AugustoS97/BMS-BatterySystem/Diseno-Electronico/CAN2Serial/RENDER/render_2.png

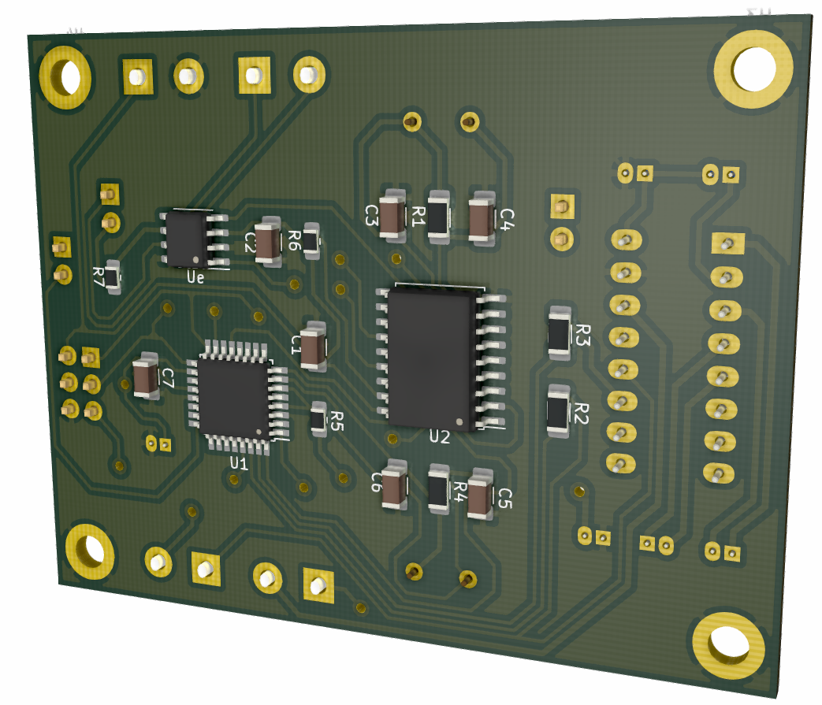
Diseno-Electronico/CAN2Serial/RENDER/render_2.png
