AugustoS97/BMS-BatterySystem/Diseno-Electronico/EPSolar-CAN/RENDER/render_2.png

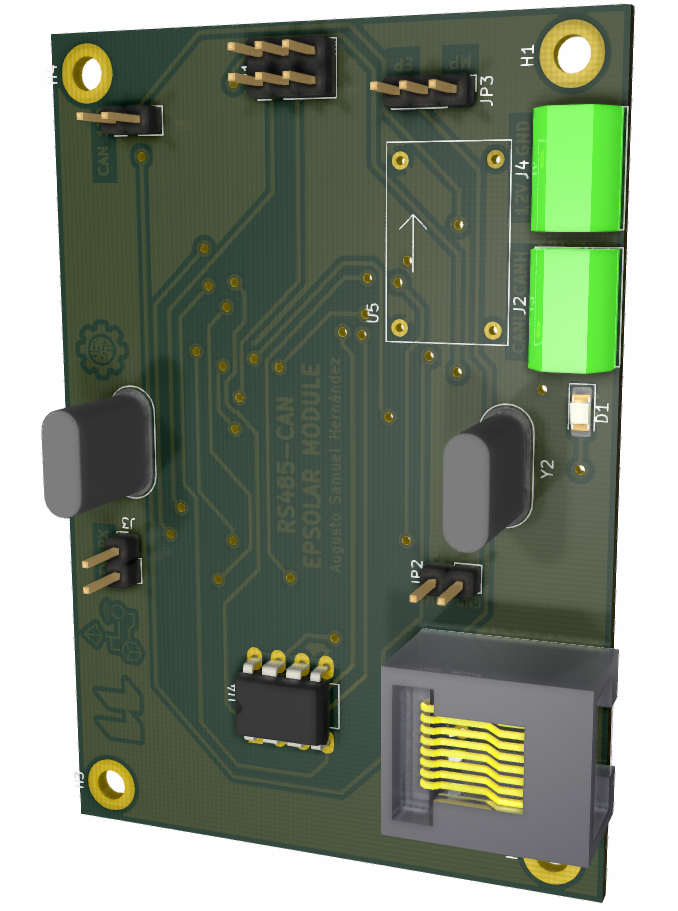
Diseno-Electronico/EPSolar-CAN/RENDER/render_2.png
