AugustoS97/BMS-BatterySystem/Diseno-Electronico/SmartBMS/RENDER/bms_render_top.png

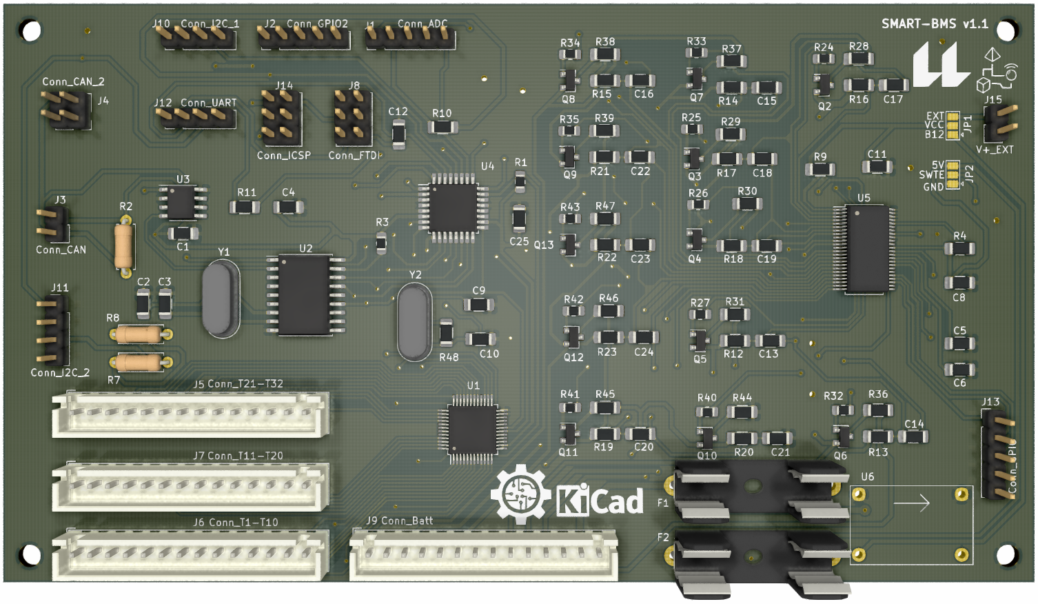
Diseno-Electronico/SmartBMS/RENDER/bms_render_top.png
