AugustoS97/BMS-BatterySystem/Diseno-Electronico/SmartBMS/RENDER/render_0.jpg

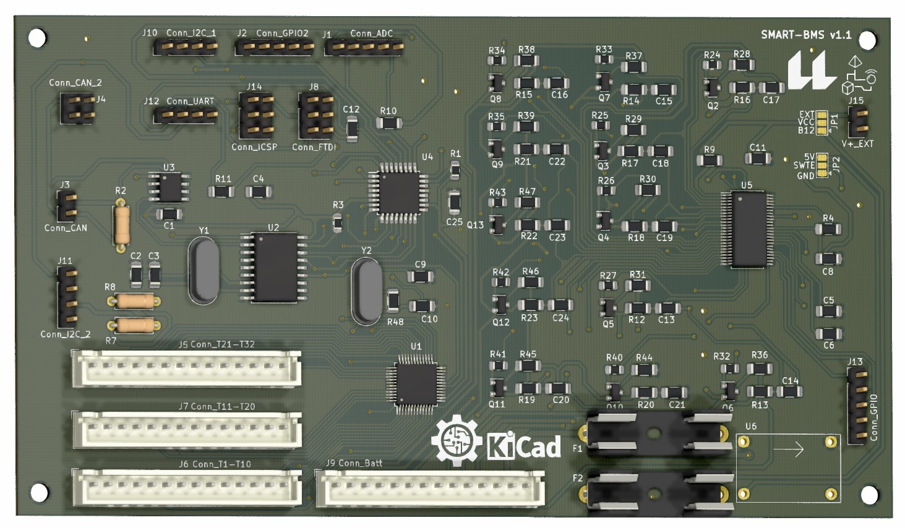
Diseno-Electronico/SmartBMS/RENDER/render_0.jpg
