AugustoS97/BMS-BatterySystem/Diseno-Electronico/SmartBMS/RENDER/render_2.jpg

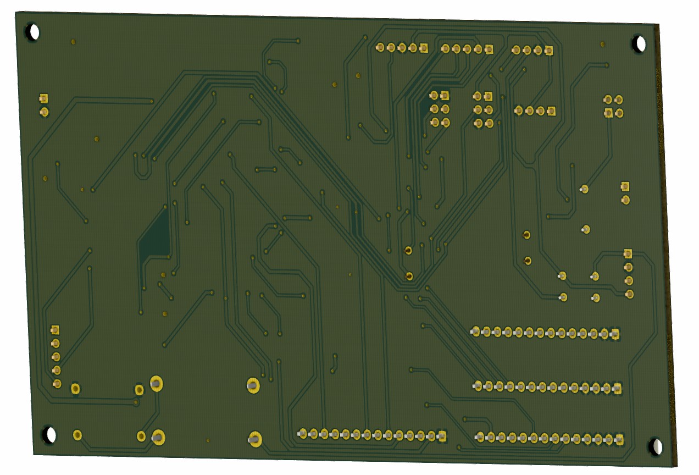
Diseno-Electronico/SmartBMS/RENDER/render_2.jpg
