AugustoS97/BMS-BatterySystem/img/bms_transparente.png

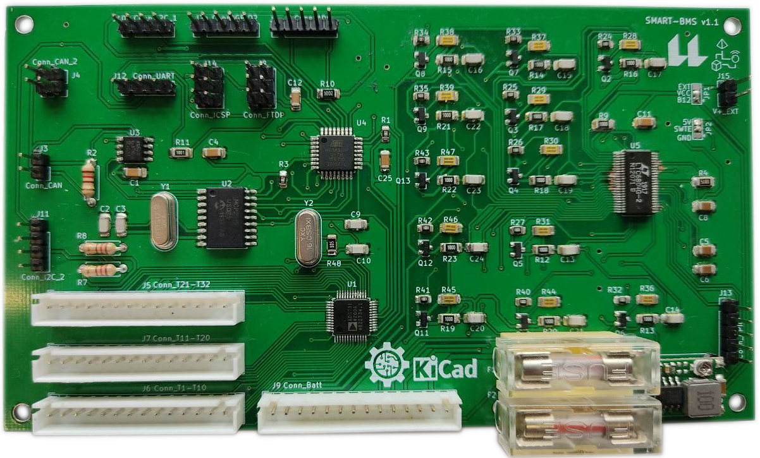
img/bms_transparente.png
