AugustoS97/BMS-BatterySystem/img/nodo_portatil_captura.png

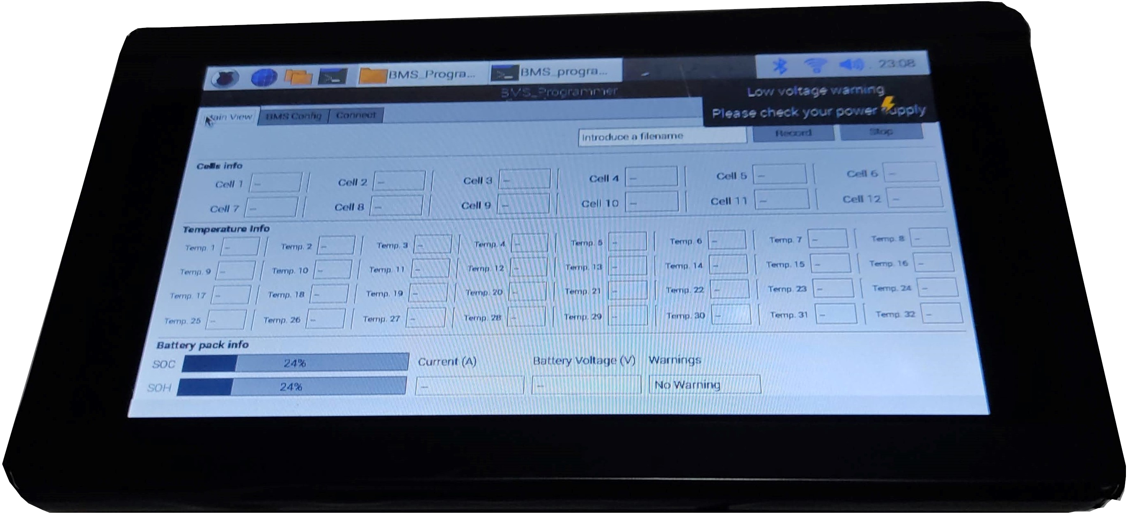
img/nodo_portatil_captura.png
