AugustoS97/BMS-BatterySystem/Software/bms_data_processing/figures/11Ohm/20210805_differencevolt.png

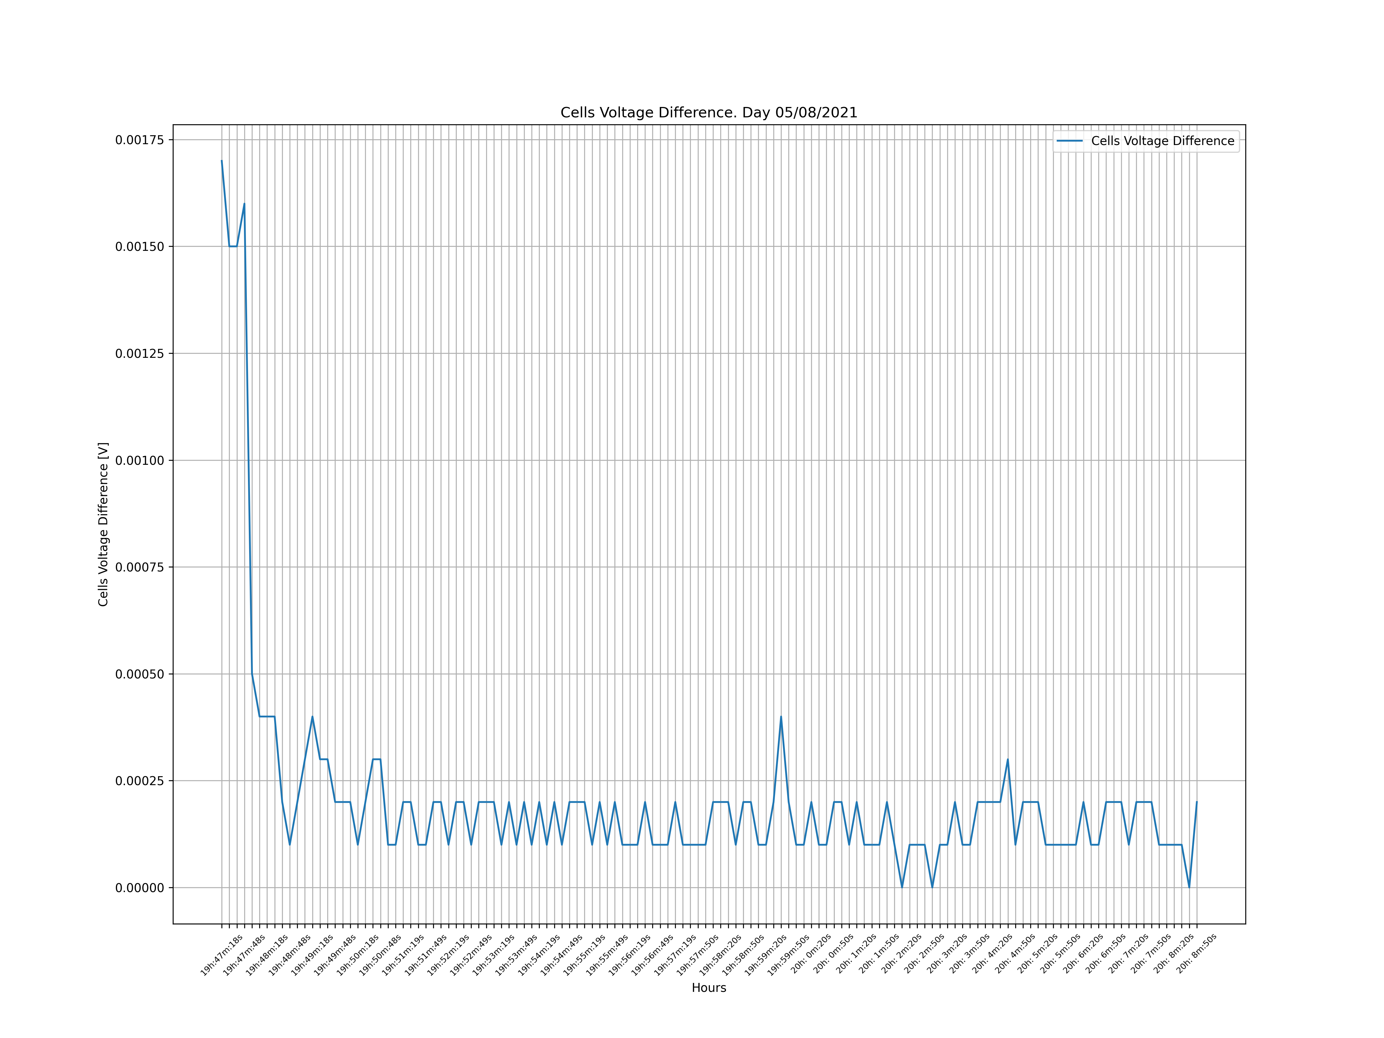
Software/bms_data_processing/figures/11Ohm/20210805_differencevolt.png
