AugustoS97/BMS-BatterySystem/Software/bms_data_processing/figures/44Ohm/20210805_temp_3.png

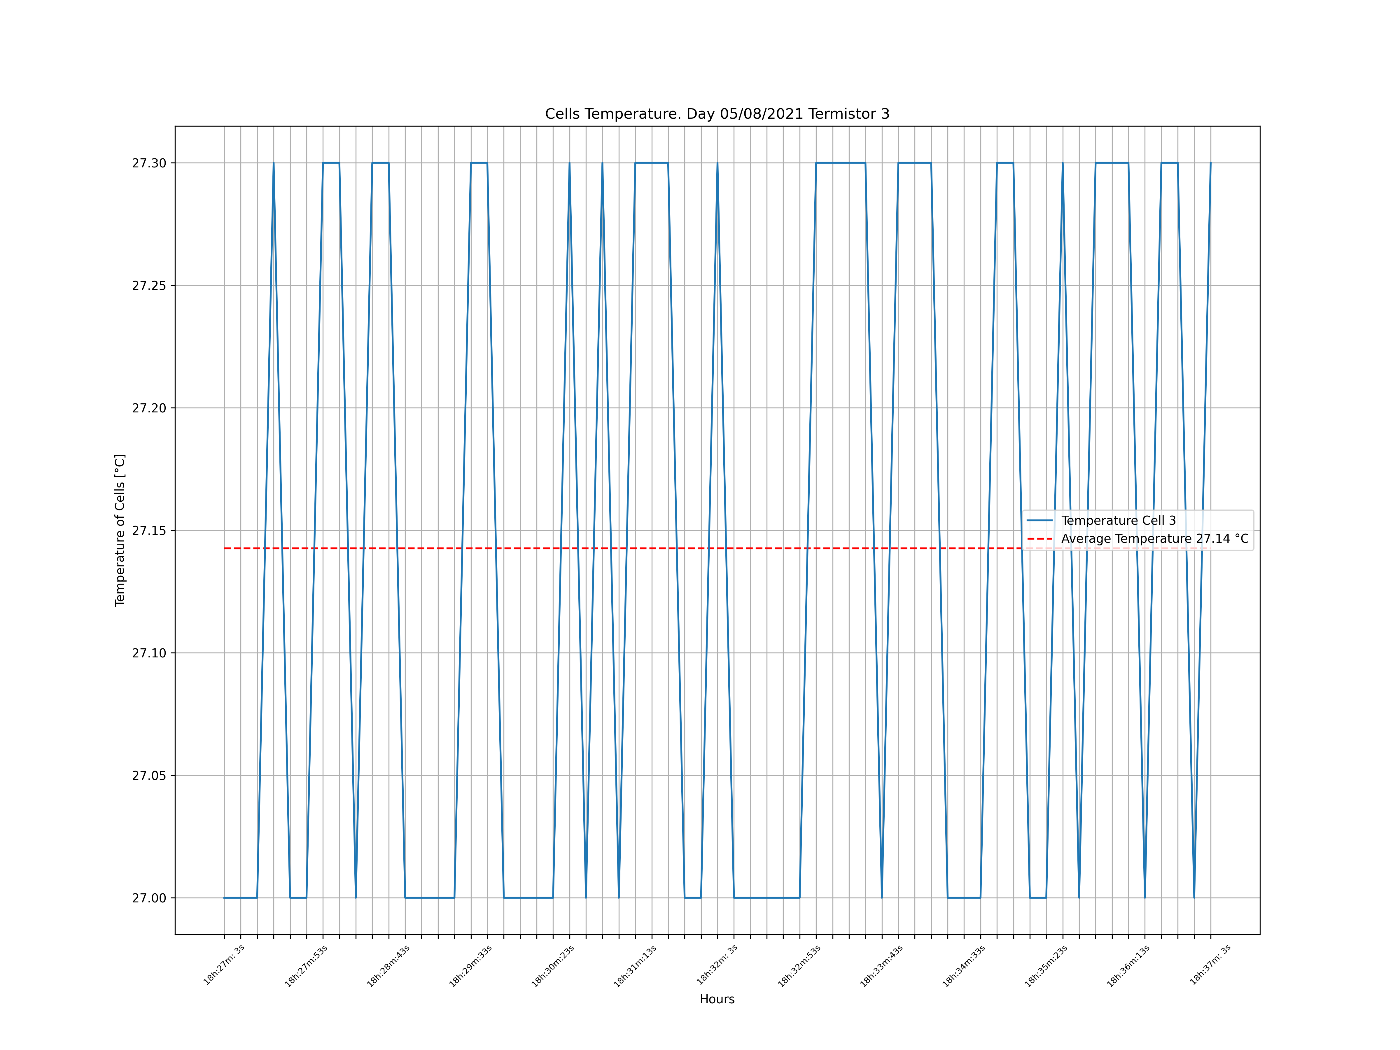
Software/bms_data_processing/figures/44Ohm/20210805_temp_3.png
