AugustoS97/BMS-BatterySystem/Software/bms_data_processing/figures/carga_15A/20210811_current.png

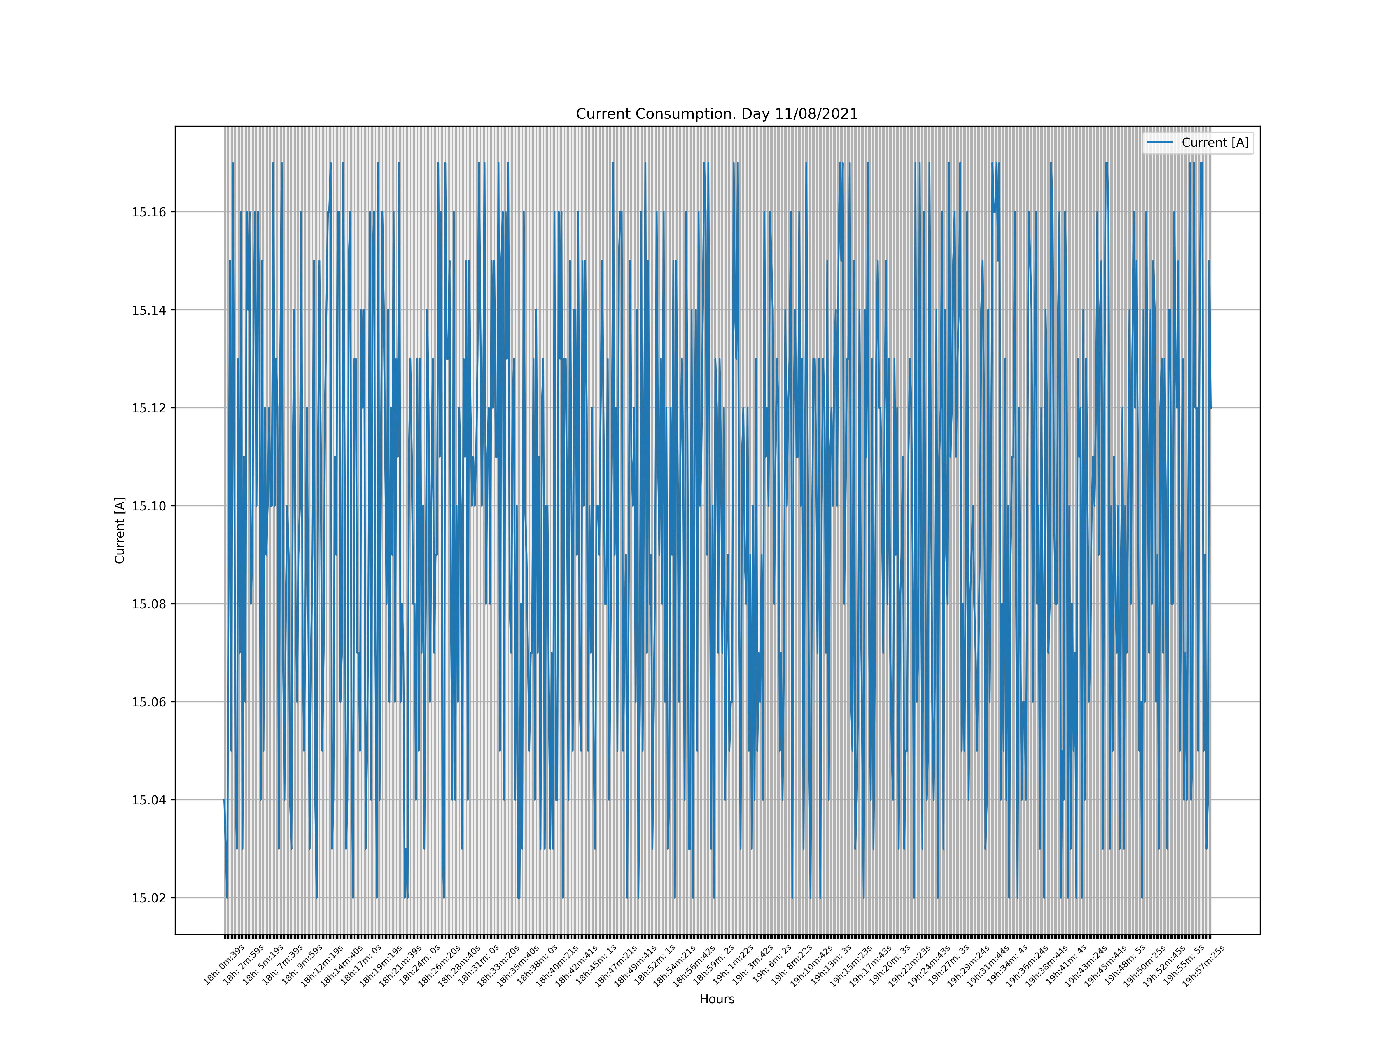
Software/bms_data_processing/figures/carga_15A/20210811_current.png
