AugustoS97/BMS-BatterySystem/Software/bms_data_processing/figures/descarga_10A/20210809_temp_1.png

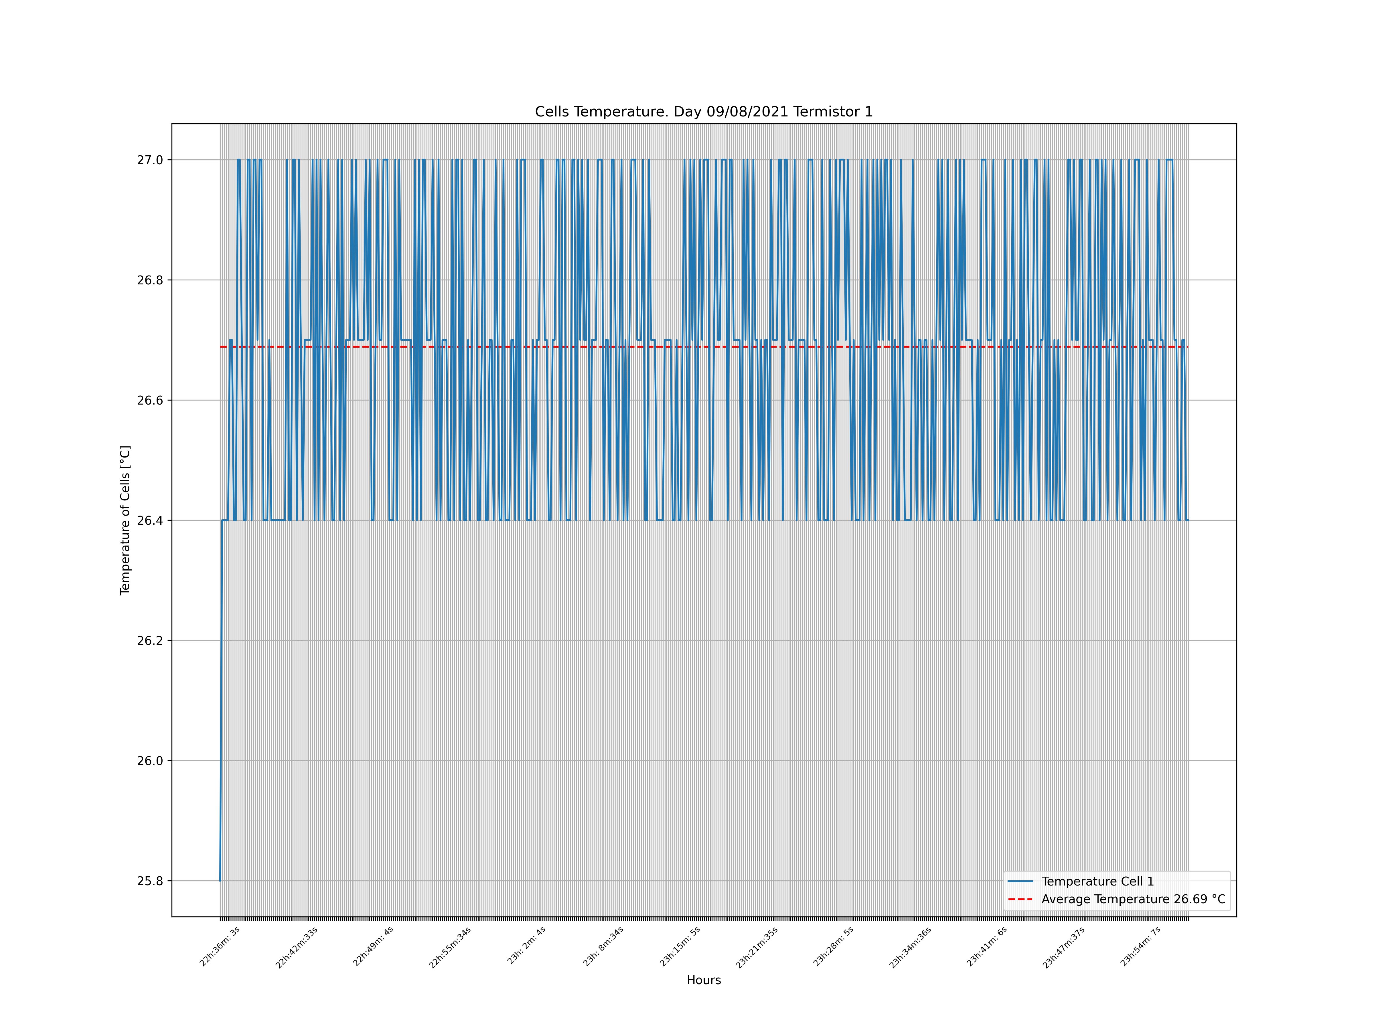
Software/bms_data_processing/figures/descarga_10A/20210809_temp_1.png
