AugustoS97/BMS-BatterySystem/Software/power_data_processing/data/A2021/M04/D12/20210412_voltage.png

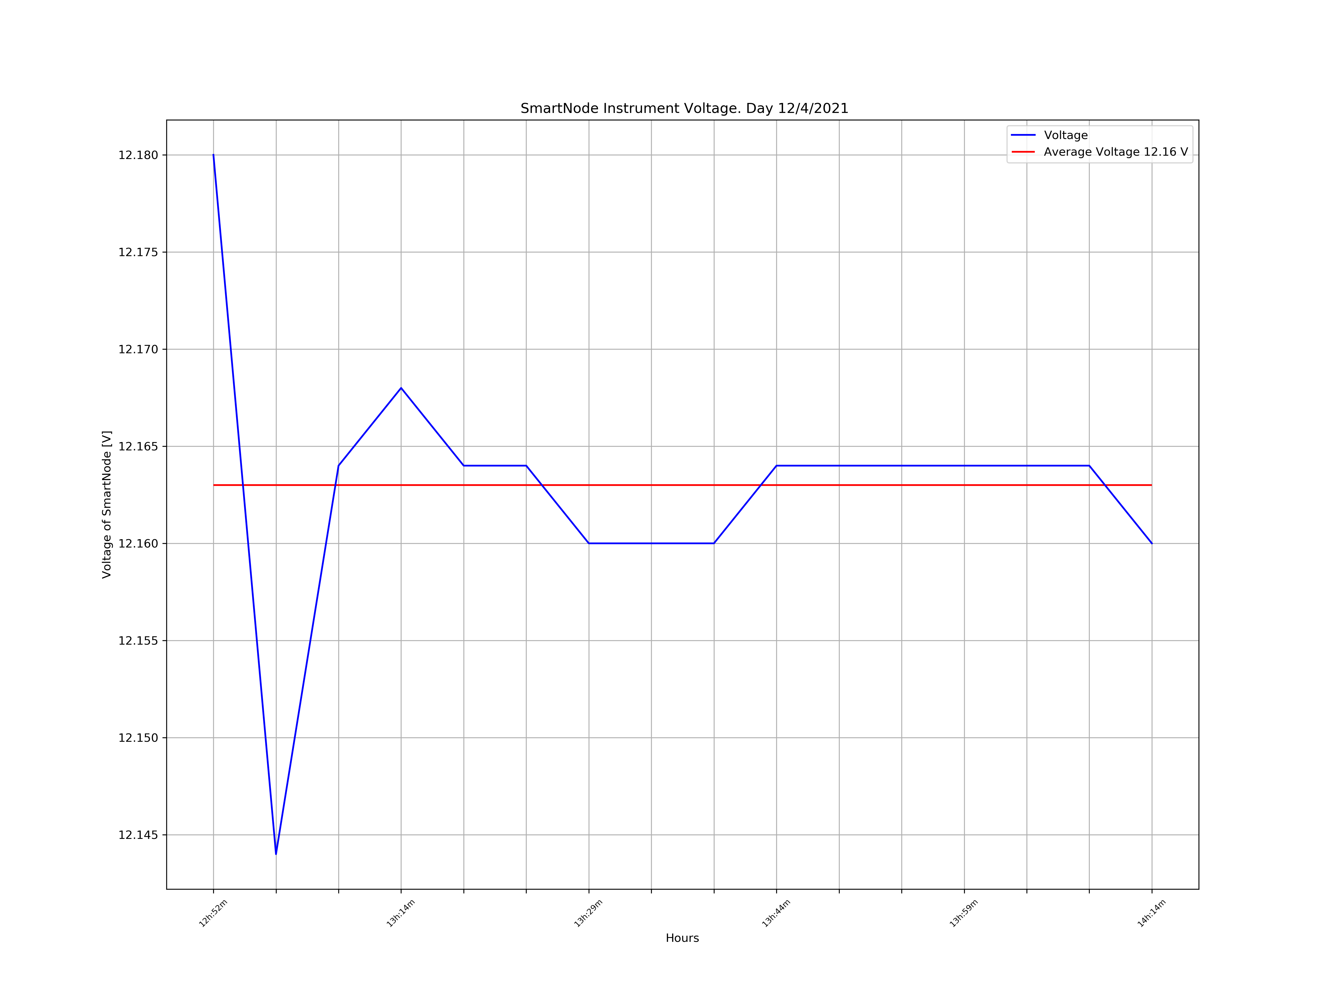
Software/power_data_processing/data/A2021/M04/D12/20210412_voltage.png
