AugustoS97/BMS-BatterySystem/Software/power_data_processing/data/A2021/M04/D14/20210414_temp.png

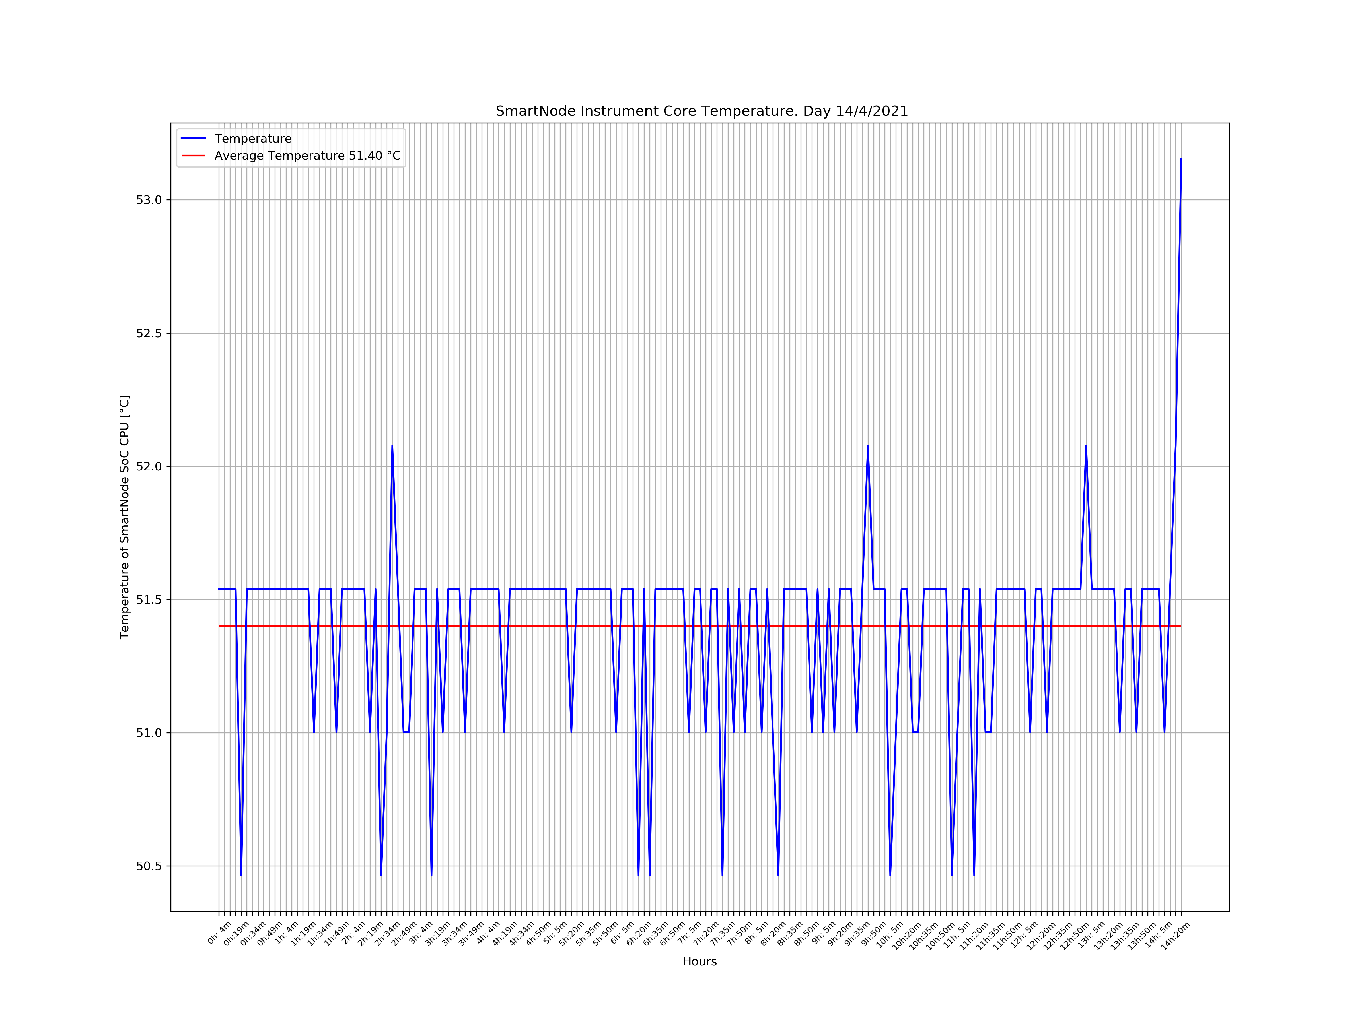
Software/power_data_processing/data/A2021/M04/D14/20210414_temp.png
