AugustoS97/BMS-BatterySystem/Software/power_data_processing/data/A2021/M04/D21/20210421_temp.png

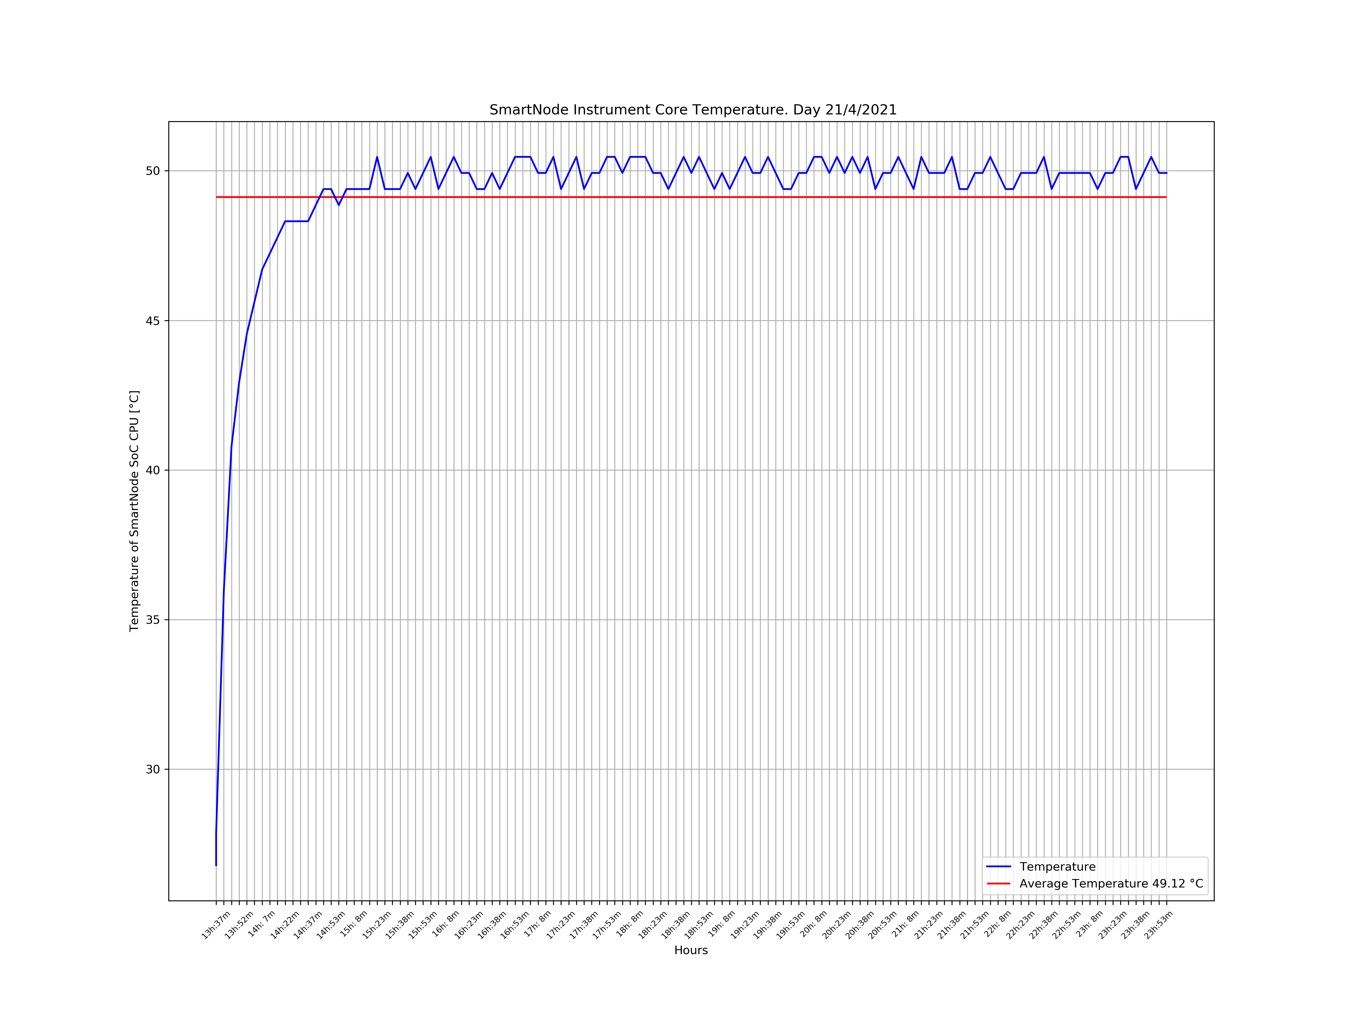
Software/power_data_processing/data/A2021/M04/D21/20210421_temp.png
