AugustoS97/BMS-BatterySystem/Software/power_data_processing/data/A2021/M04/D22/20210422_current.png

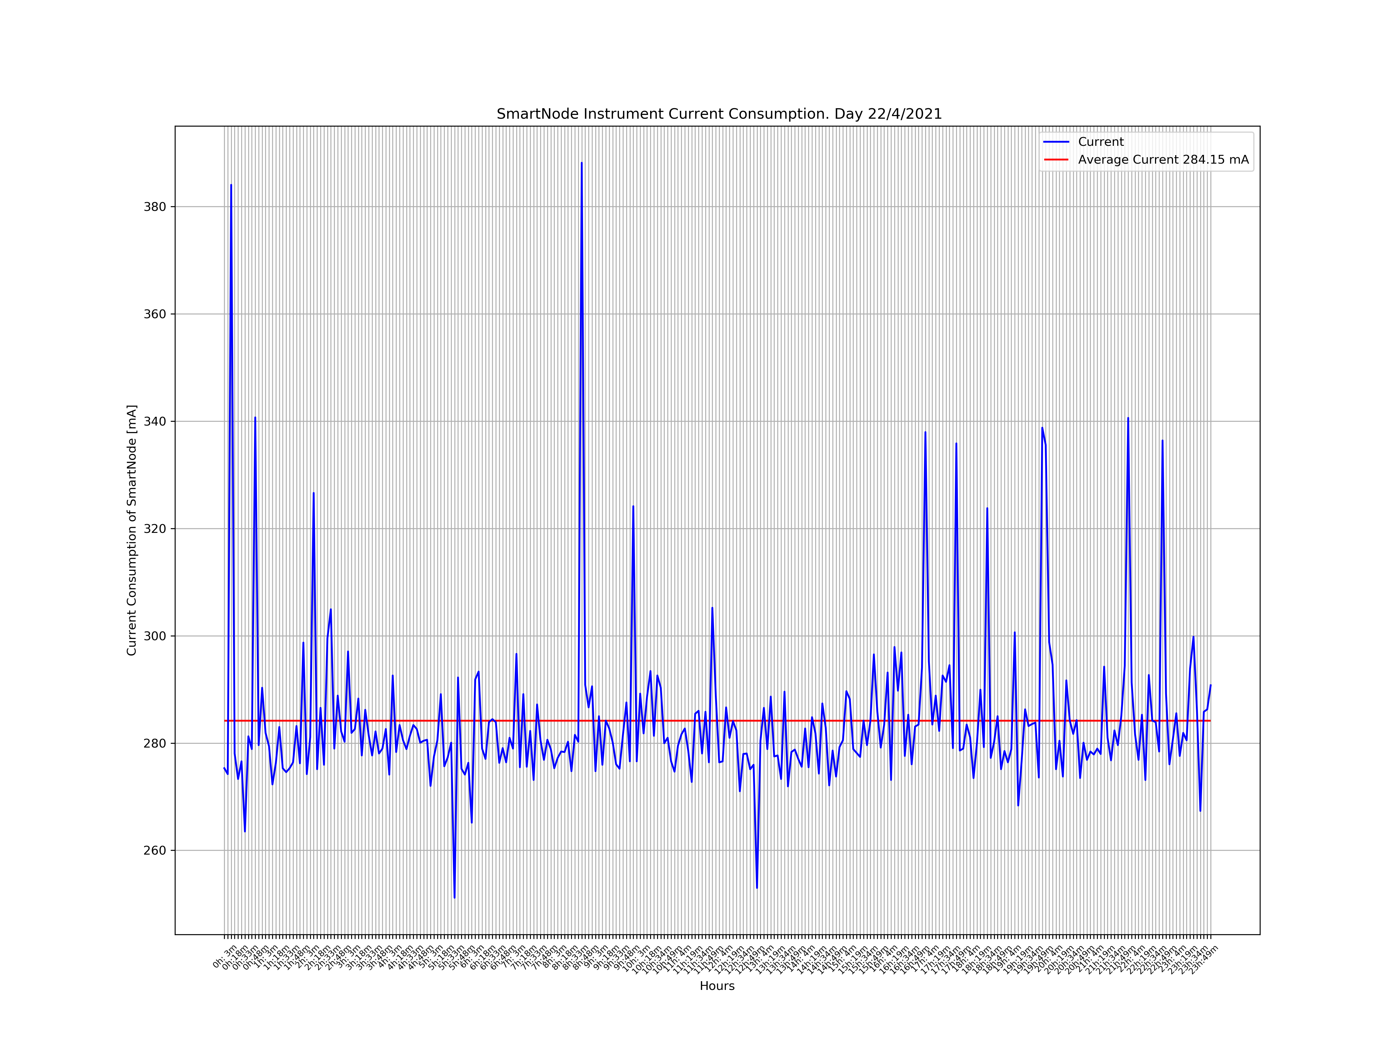
Software/power_data_processing/data/A2021/M04/D22/20210422_current.png
