AugustoS97/BMS-BatterySystem/Software/power_data_processing/data/A2021/M04/D26/20210426_current.png

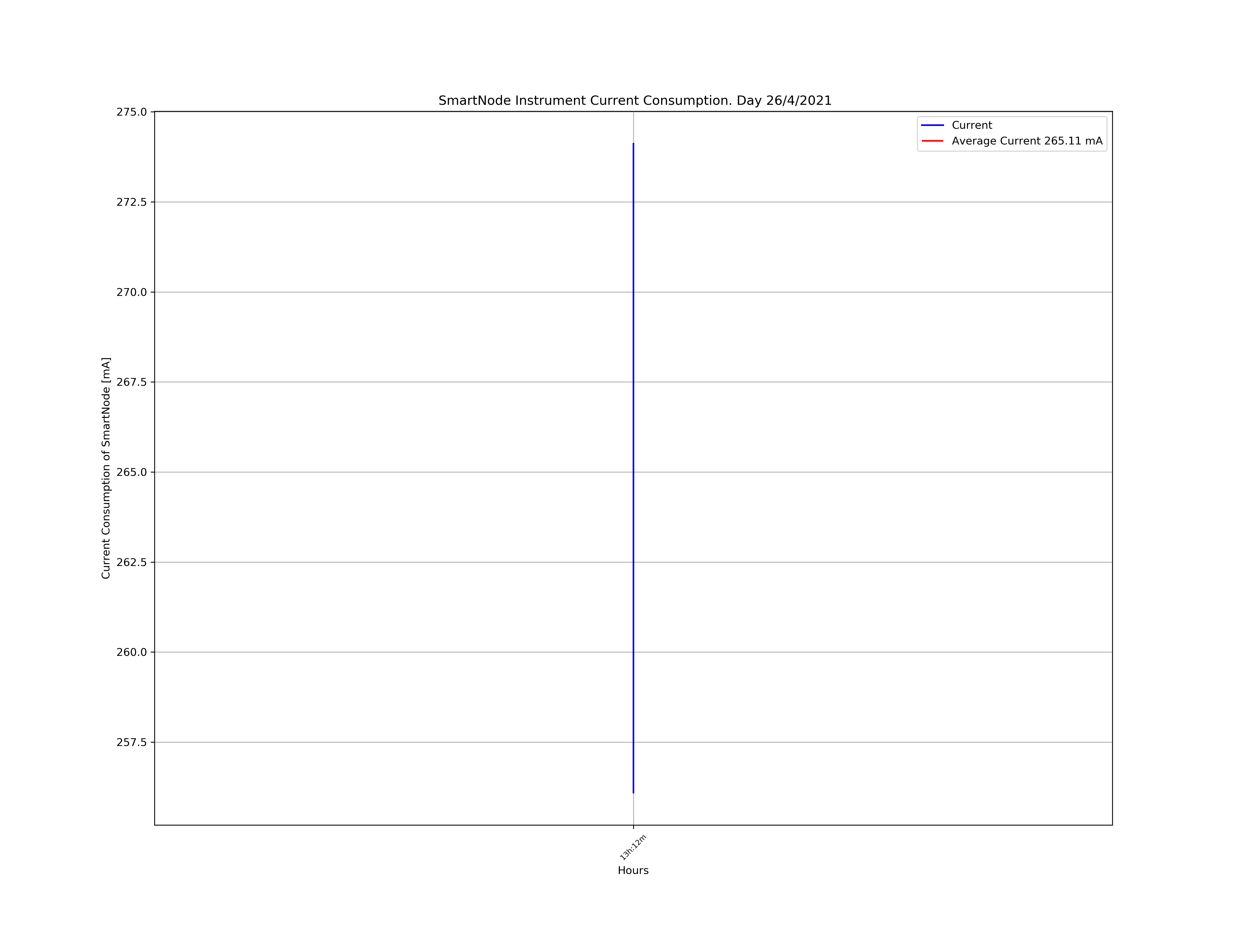
Software/power_data_processing/data/A2021/M04/D26/20210426_current.png
