AugustoS97/BMS-BatterySystem/Software/power_data_processing/data/A2021/M04/D27/20210427_voltage.png

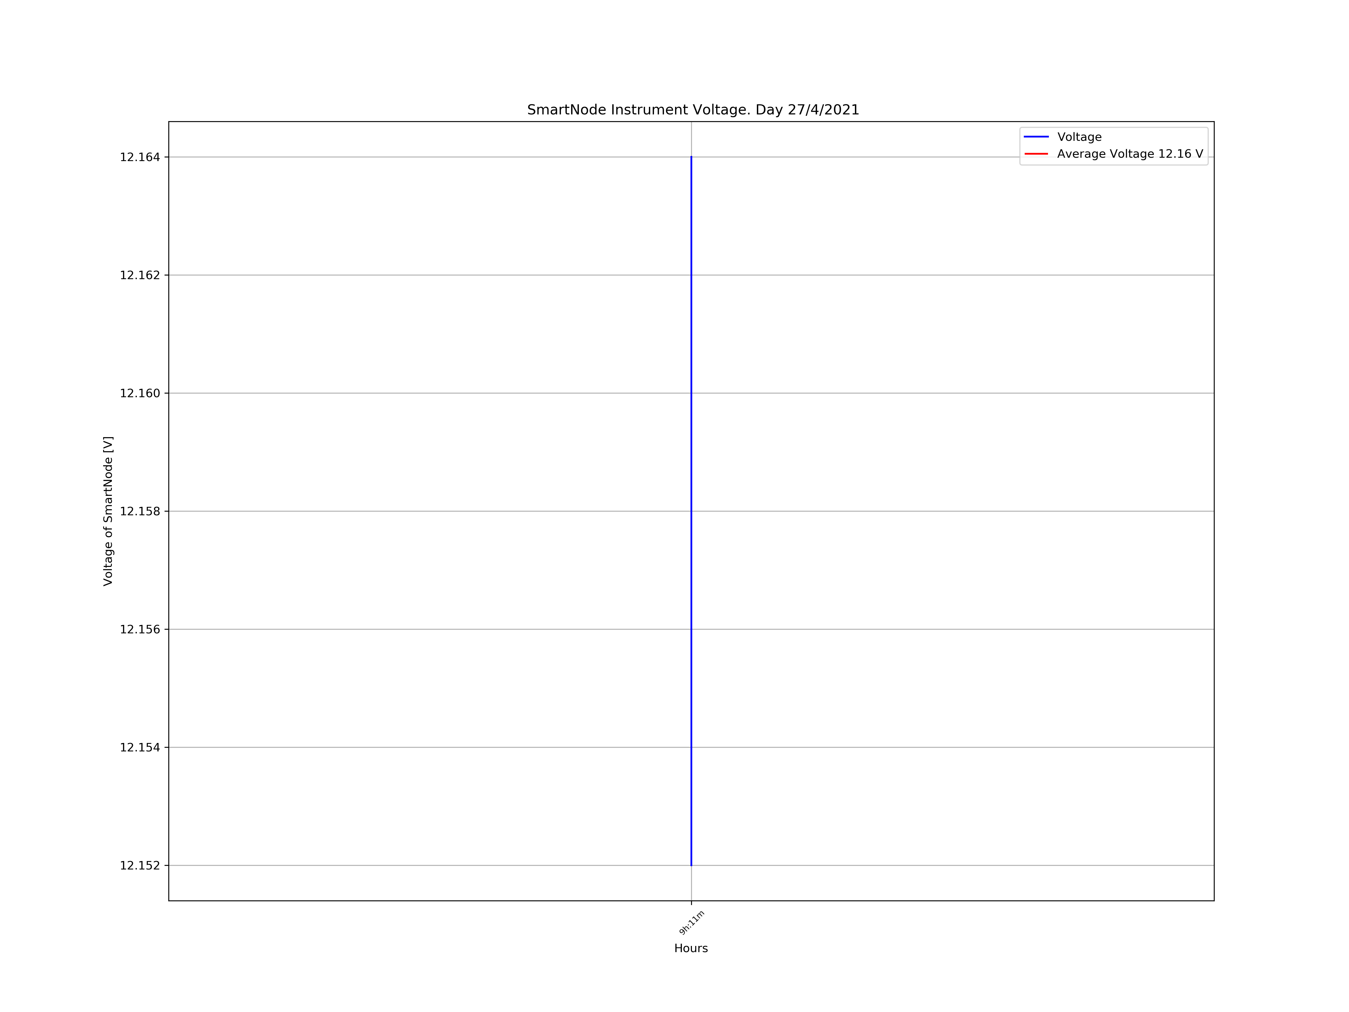
Software/power_data_processing/data/A2021/M04/D27/20210427_voltage.png
