AugustoS97/BMS-BatterySystem/Software/SOC_estimation/figures/ensayo1/SOC_empirical.png

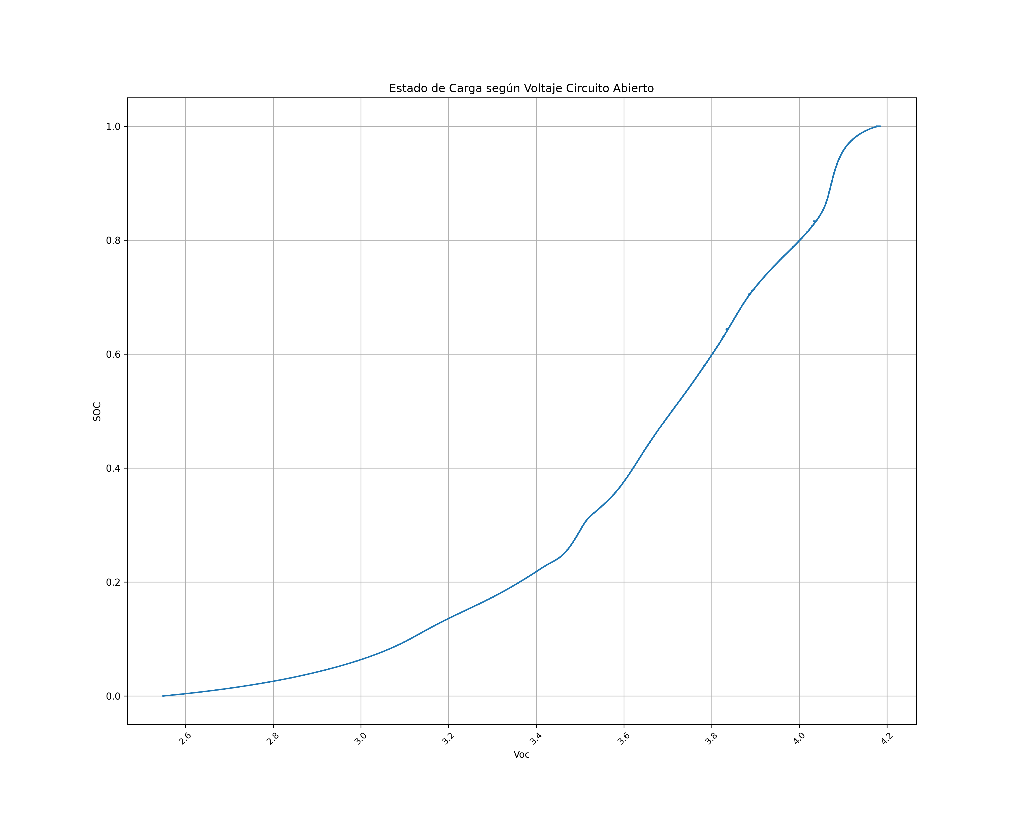
Software/SOC_estimation/figures/ensayo1/SOC_empirical.png
