AugustoS97/BMS-BatterySystem/Software/SOC_estimation/figures/ensayo1/SOC_polynomical_2_to_8.png

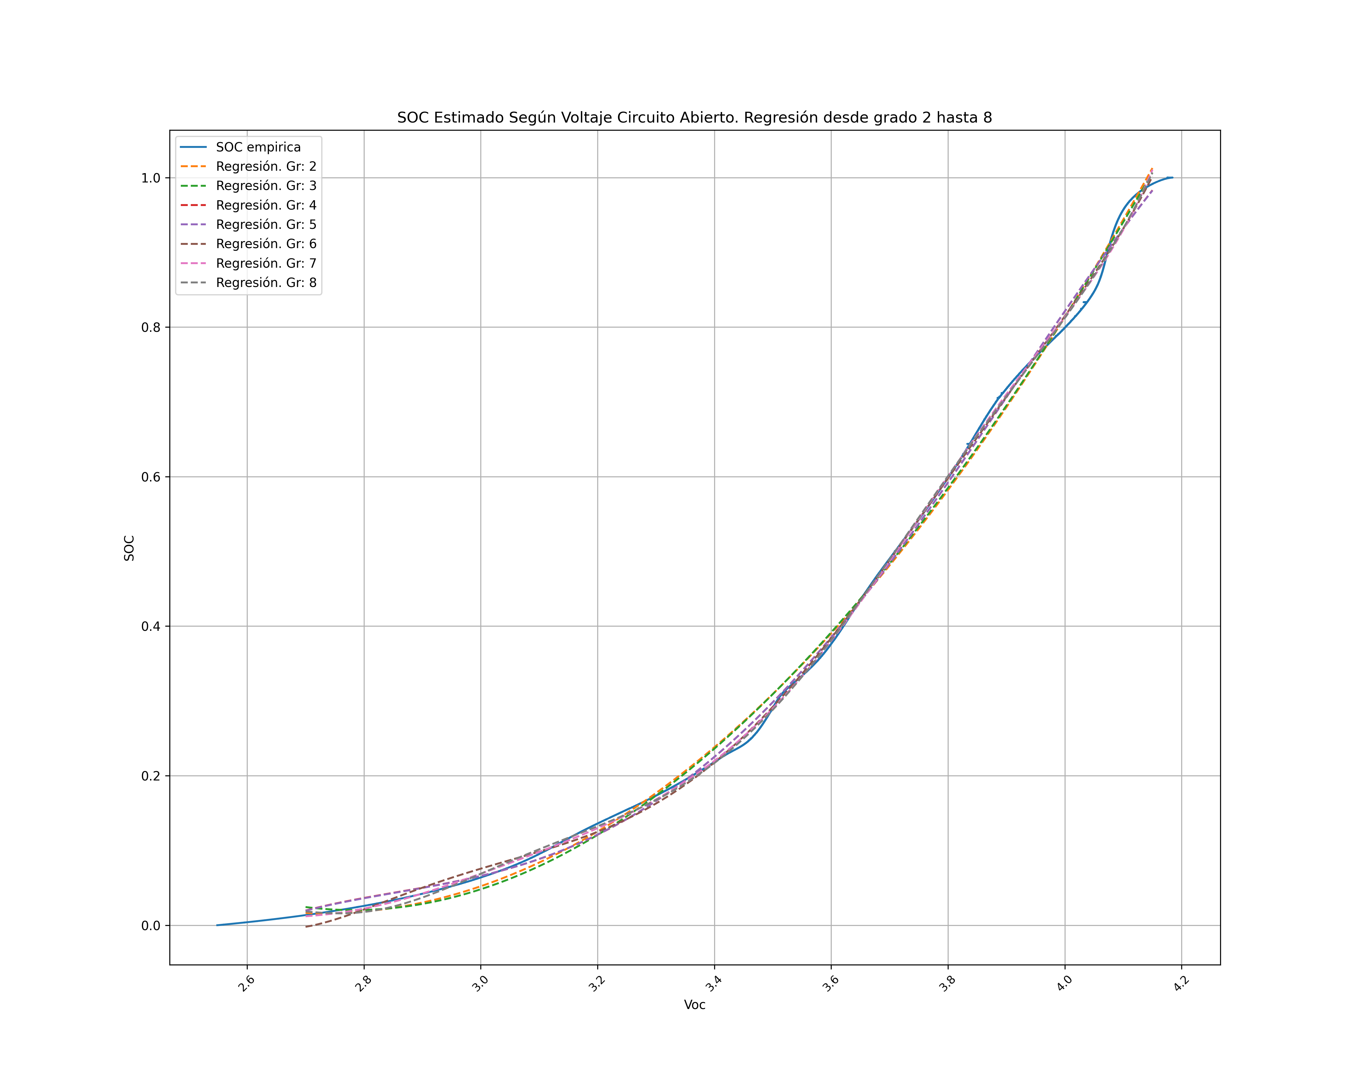
Software/SOC_estimation/figures/ensayo1/SOC_polynomical_2_to_8.png
