AugustoS97/BMS-BatterySystem/Software/SOC_estimation/figures/ensayo3/SOC_regretion_degree_2.png

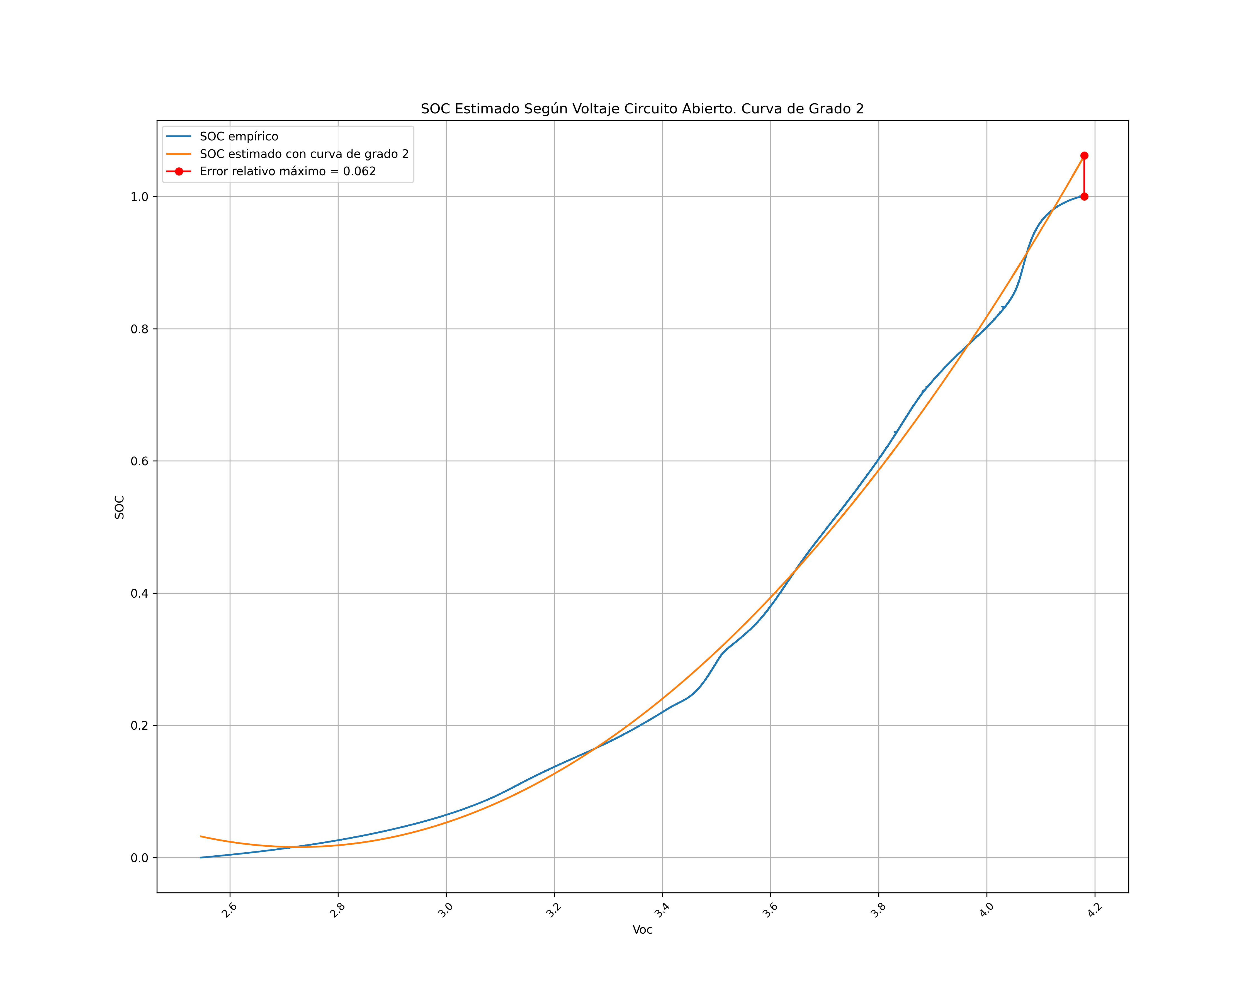
Software/SOC_estimation/figures/ensayo3/SOC_regretion_degree_2.png
